Pierregmd/Angular-sensor-using-gray-code/media/tmp_2ec697d3-8678-4523-a3d9-68ab7ae980d0.jpeg

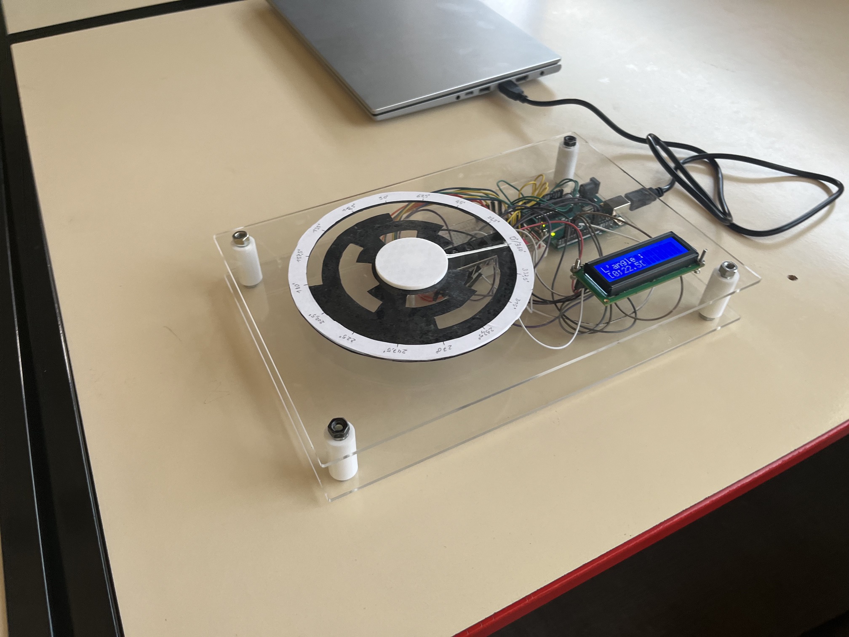
media/tmp_2ec697d3-8678-4523-a3d9-68ab7ae980d0.jpeg
