Pierregmd/Angular-sensor-using-gray-code/media/tmp_9601a93d-c5cf-43fe-bc41-4c7ea73003b8.jpeg

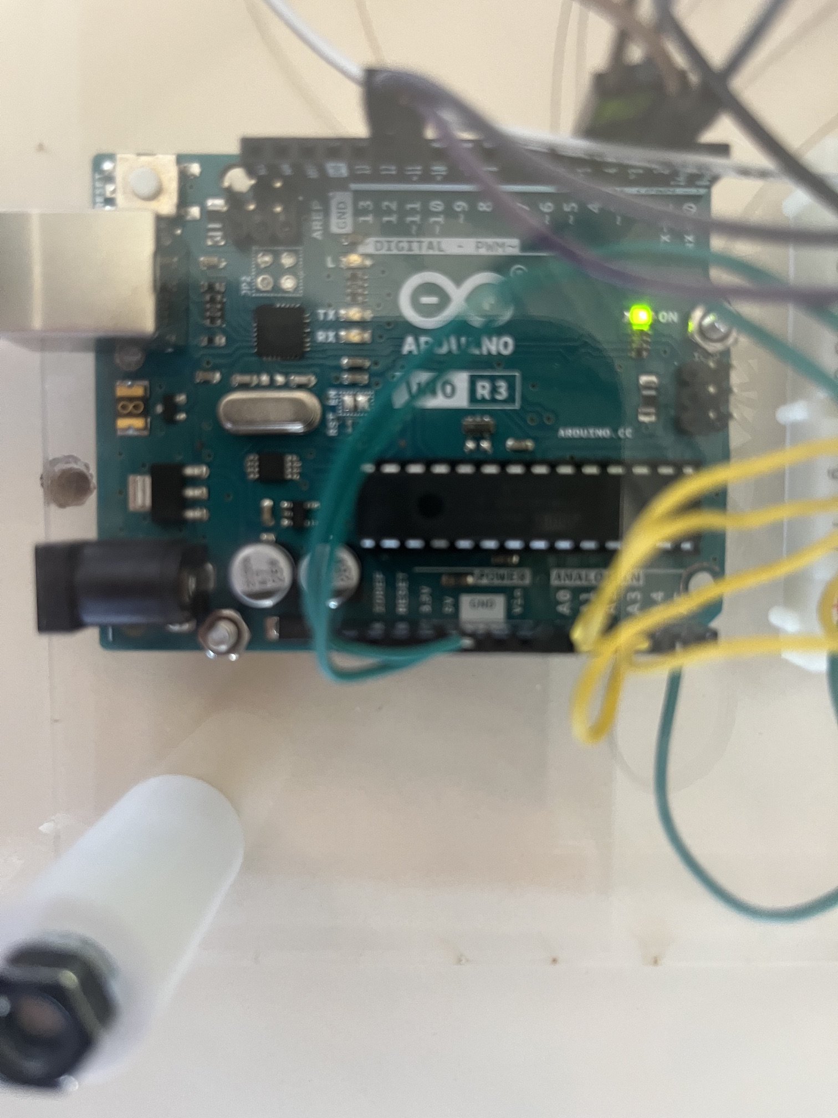
media/tmp_9601a93d-c5cf-43fe-bc41-4c7ea73003b8.jpeg
