Pierregmd/Angular-sensor-using-gray-code/media/tmp_b2613c18-2cb0-4952-9ea2-55c562d0ac82.jpeg

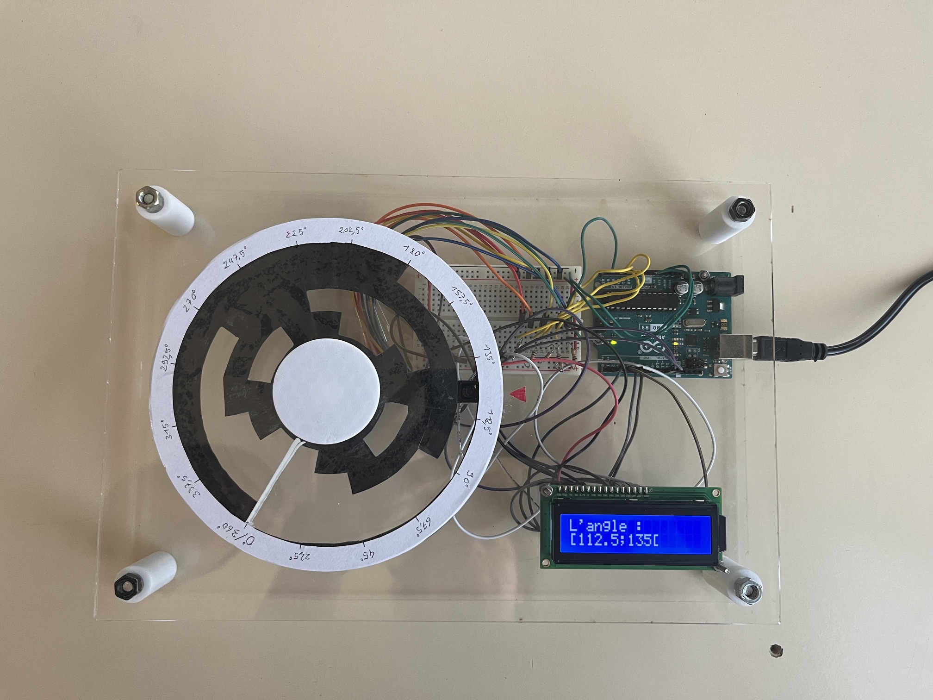
media/tmp_b2613c18-2cb0-4952-9ea2-55c562d0ac82.jpeg
