Pierregmd/Angular-sensor-using-gray-code/media/tmp_f0d8ab9e-5268-4787-9d54-c83a04ad6275.jpeg

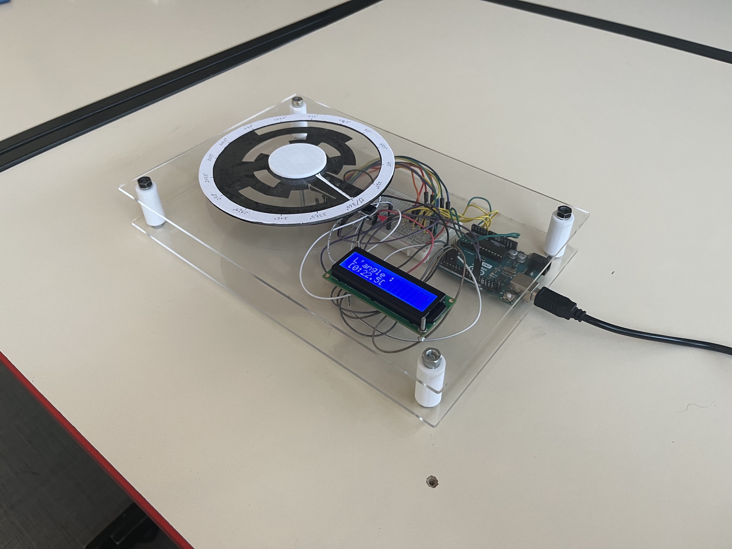
media/tmp_f0d8ab9e-5268-4787-9d54-c83a04ad6275.jpeg
