Pierregmd/Angular-sensor-using-gray-code/media/tmp_ff19b213-c176-42c7-b046-29f1a3fe3b53.jpeg

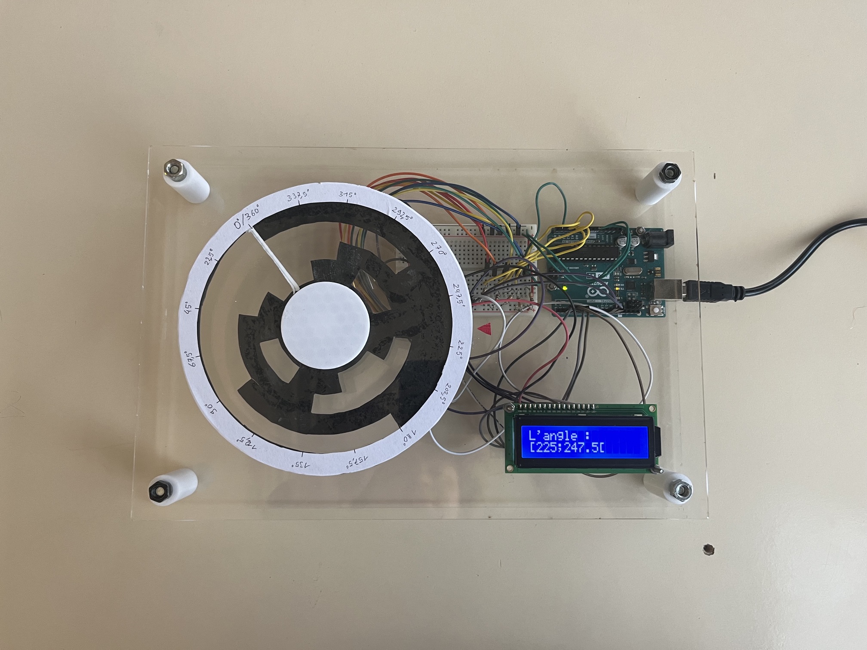
media/tmp_ff19b213-c176-42c7-b046-29f1a3fe3b53.jpeg
