Pierregmd/Angular-sensor-using-gray-code/media/20260507_192013.jpg

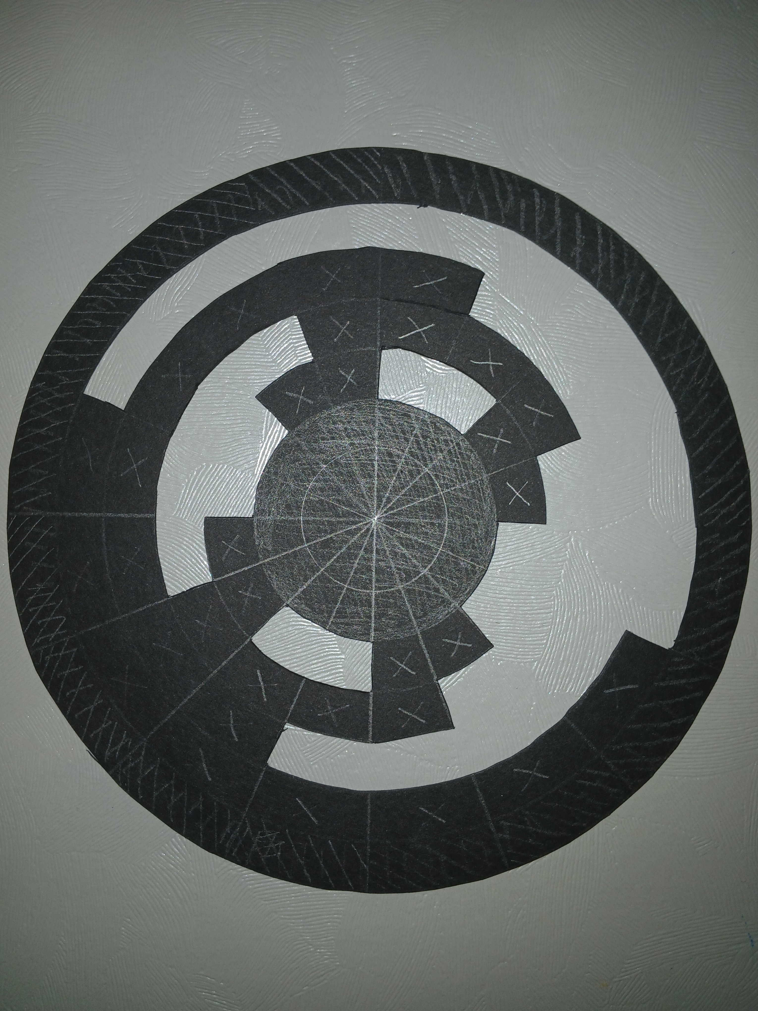
media/20260507_192013.jpg
